Punkcl0/PageStomp_Pedal/img/IMG_8121.jpeg

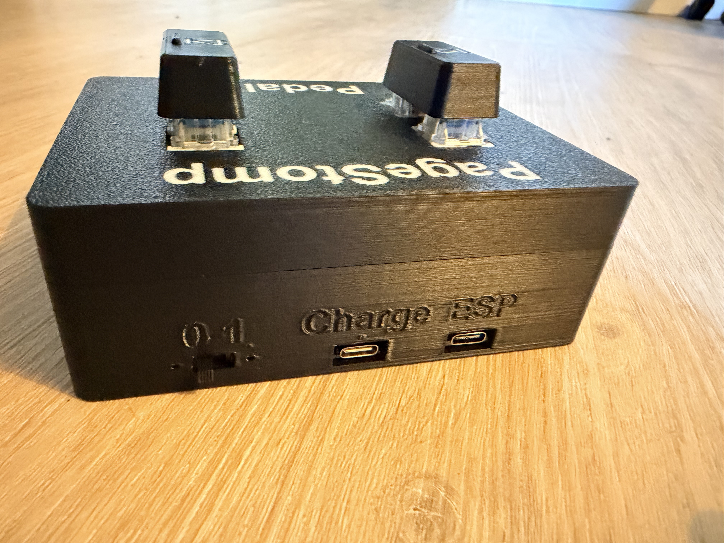
img/IMG_8121.jpeg
