Punkcl0/PageStomp_Pedal/img/IMG_8122.jpeg

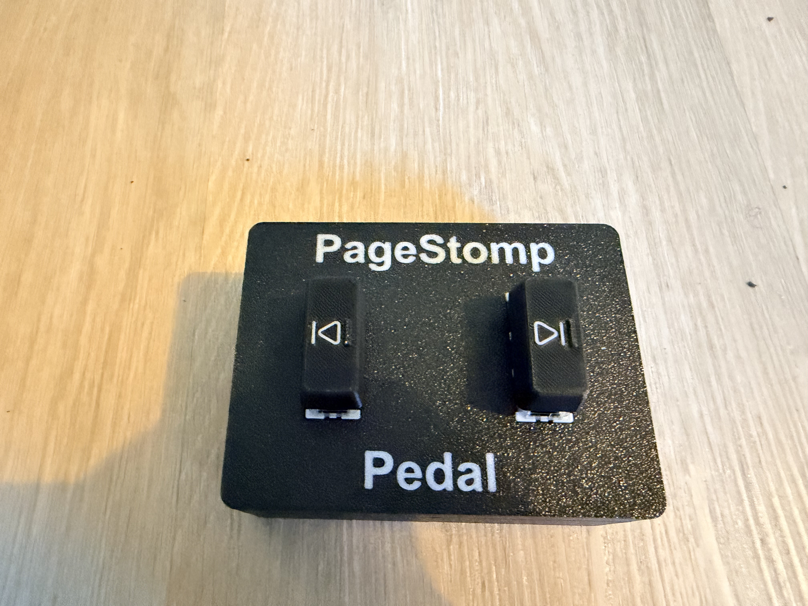
img/IMG_8122.jpeg
