Punkcl0/PageStomp_Pedal/img/IMG_8123.jpeg

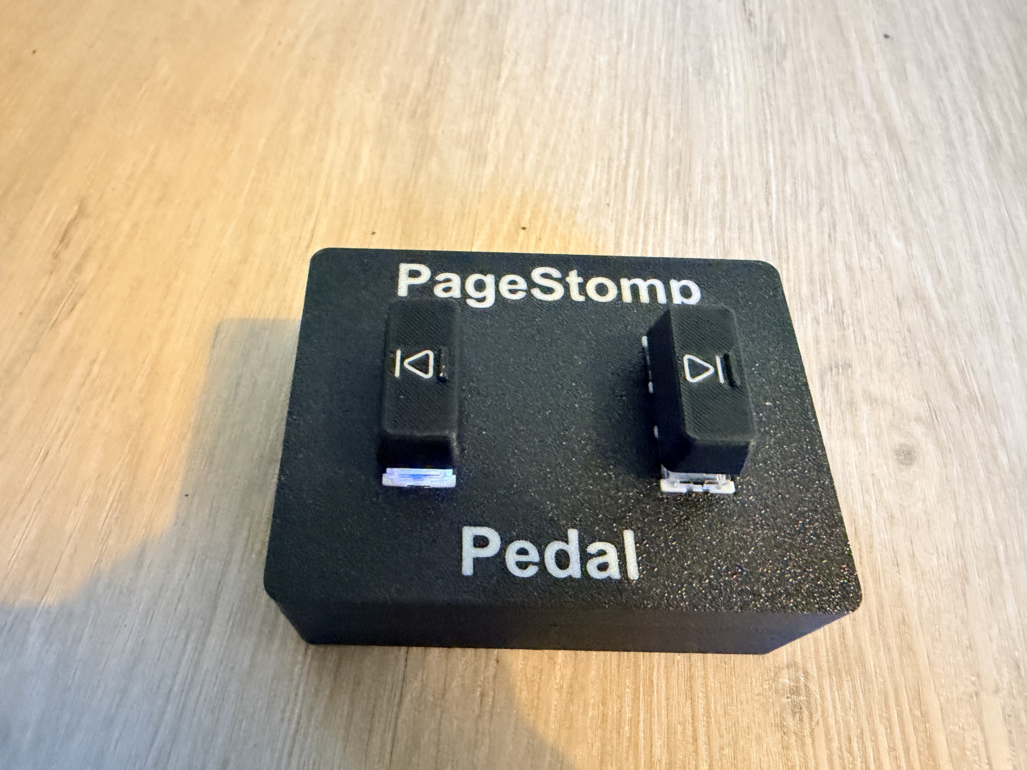
img/IMG_8123.jpeg
