Punkcl0/PageStomp_Pedal/img/IMG_8116.jpeg

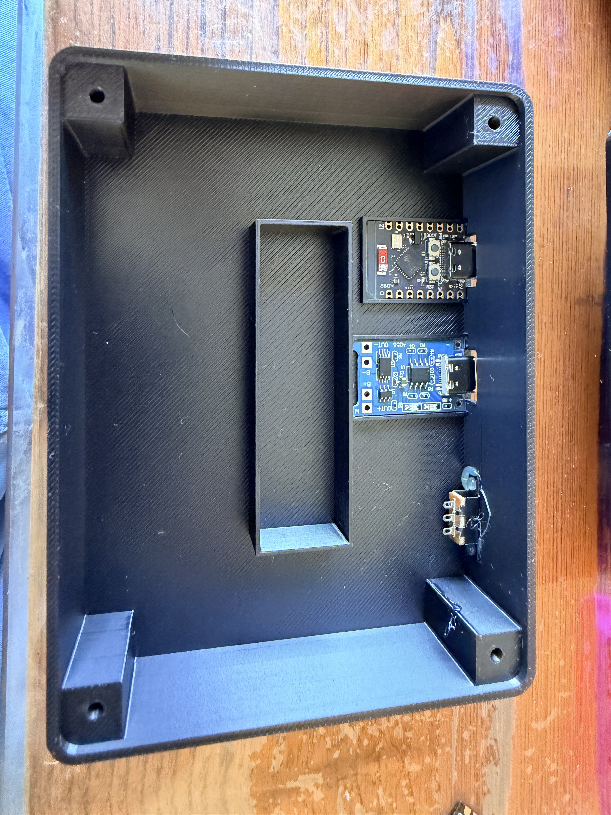
img/IMG_8116.jpeg
