Punkcl0/PageStomp_Pedal/img/IMG_8117.jpeg

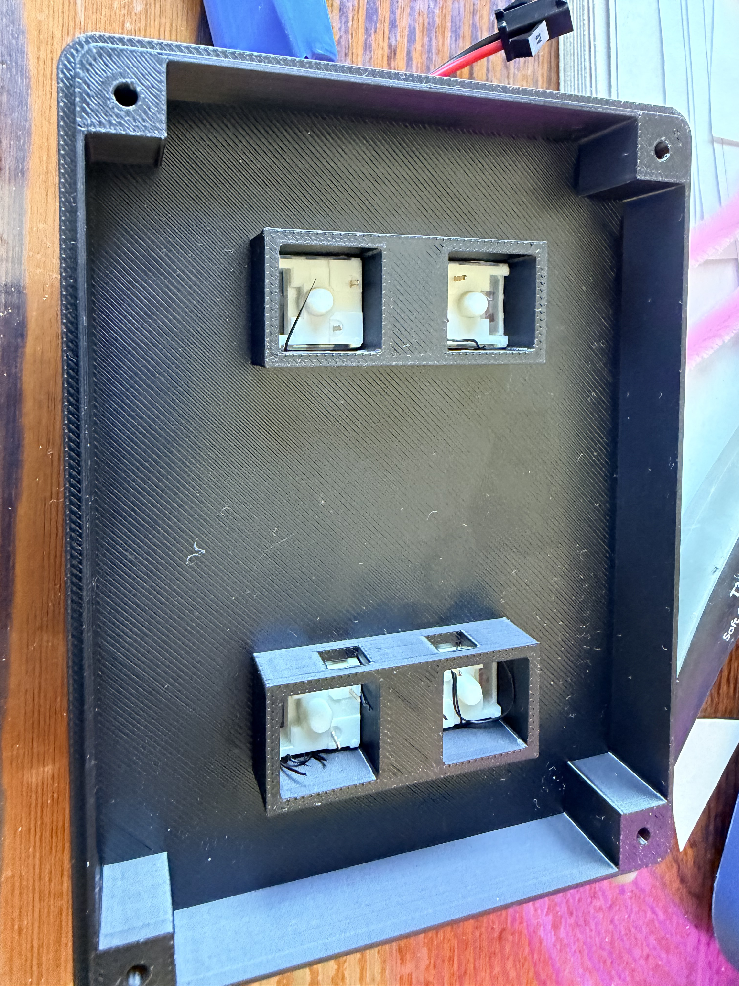
img/IMG_8117.jpeg
