Punkcl0/PageStomp_Pedal/img/IMG_8118.jpeg

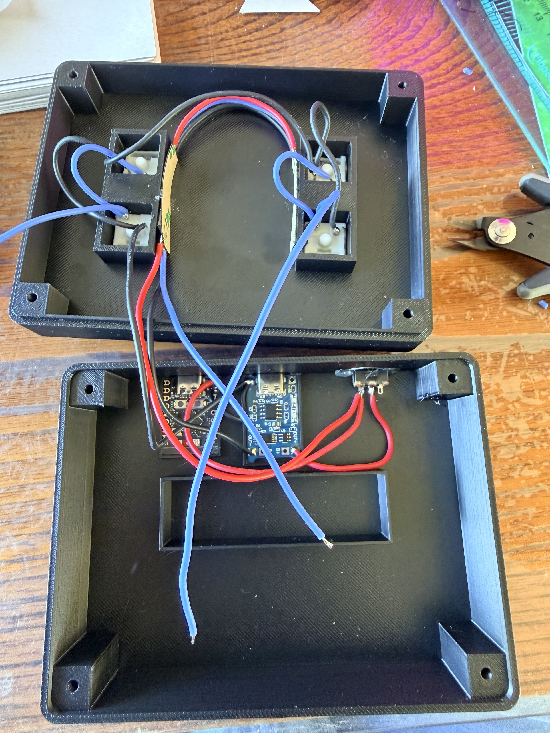
img/IMG_8118.jpeg
